Kybernetika-SPSE/RP_Psutka_Slepicka/škola_info/reporty/Slepička/2024_12_20.pdf

# RP report

Frantiˇsek Slepiˇcka

20.12.2024

Aktu´alnˇe m´ame jen jedno ESP32 (p˚ujˇcen´y) bez UWB modulu, proto pracuji na k´odu pro lokalizaci prostˇrednictv´ım WiFi (branch wifi). Vˇetˇsina k´odu je zkop´ırovan´y EPS-IDF example na wifi-scan.

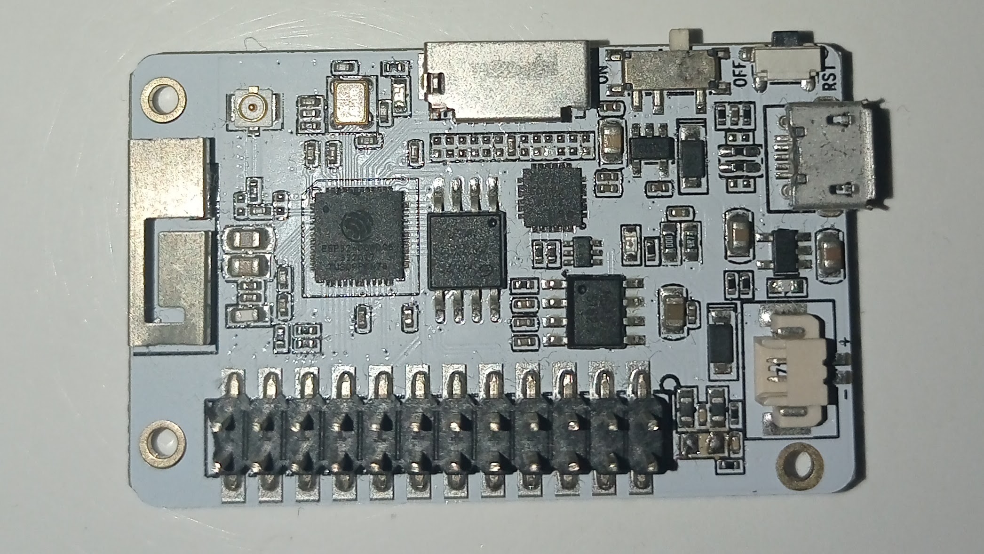
[picture p25: figure]

Figure 1: ESP

1
