Kybernetika-SPSE/RP_Psutka_Slepicka/škola_info/reporty/Slepička/2025_3_28.pdf

# RP report

František Slepička

28.3.2025

## 1 PCB

Už dorazily, takže jen zbývá nakoupit headry a nechat Matěje ať to tam napájí.

## 2 Kód

Nějak celý měsíc jsem programoval trilateraci pro navigace s UWB. Možná to nezní jako práce na celý měsíc, ale věřte mi, opravdu to zabralo celý měsíc. Všechen je na branchi wifi v RP Psutka Slepicka/src/UWB tracing logic/src/ (https://github.com/Kybernetika-SPSE/RP_Psutka_Slepicka/tree/wifi/src/UWB_tracing_logic/src) Pro samotnou trilateraci používám least square a výsledek z toho filtruji kalmanovým fitrem. Program je schopen dynamicky přepínat mezi řešením ve 2D či 3D na základě vstupních dat. Je to pravděpodobně zbytečně složité pro náš jednoduchý problém, avšak už jsem si zvykl dělat vše co nejvíc univerzální, aby to fungovalo i v jiných situacích. Tímto přístupem je projekt snadno rozšiřitelný do budoucna.

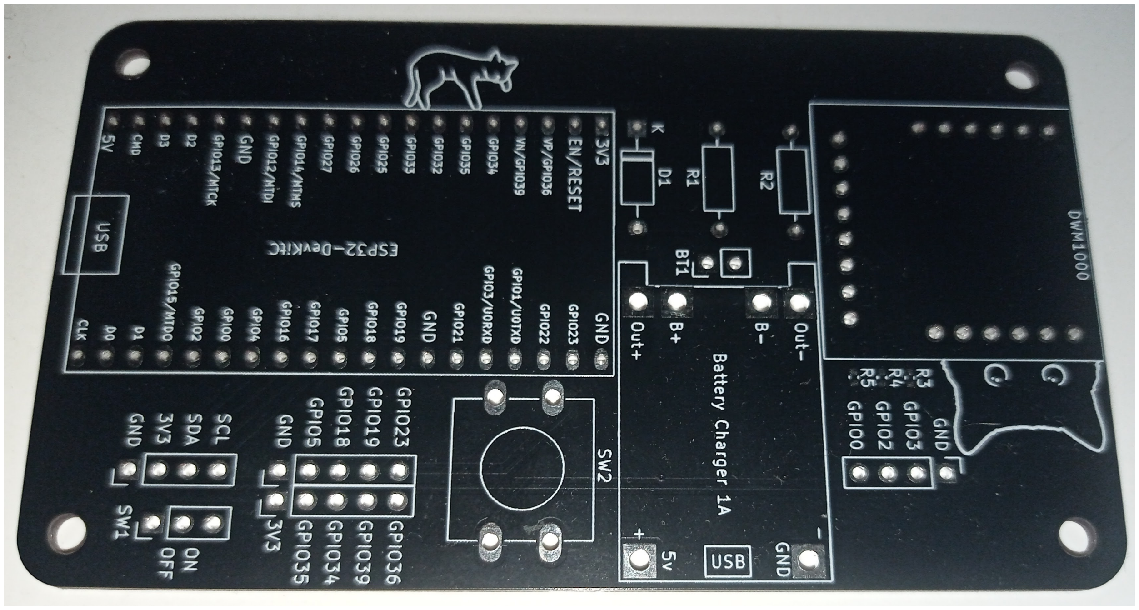
[picture p26: figure]

Figure 1: PCB

1
