Kybernetika-SPSE/RP_Psutka_Slepicka/src/main/src/serial_control/serial_control.h

#ifndef SERIAL_CONTROL_H
#define SERIAL_CONTROL_H
#include <Arduino.h>
#include "config.h"
#include "UWB_tracking_logic/trilateration.h"
#include "wifi_connection/wifi_connection.h"
#include "wifi_location/wifi_location.h"
#include "UWB/UWB.h"

void handleSerialInput();
#endif
