Kybernetika-SPSE/RP_Psutka_Slepicka/src/main/src/UWB_tracking_logic/matrix.h

#ifndef MATRIX_H
#define MATRIX_H

#include <Arduino.h>
#include <vector>

class Matrix
{
public:
    std::vector<std::vector<float>> matrix;

    Matrix();
    Matrix(int row, int col);
    Matrix(std::vector<std::vector<float>> input);

    int rows() const;
    int cols() const;

    Matrix operator*(const Matrix &other) const;
    void operator*=(float val);
    Matrix operator*(float val) const;

    std::vector<float> &operator[](int row);
    const std::vector<float> &operator[](int row) const;
    Matrix getColumn(int colIndex) const;
    void setColumn(int colIndex, const Matrix &col);

    Matrix operator+(const Matrix &other) const;
    Matrix operator-(const Matrix &other) const;

    void print() const;

    void set_value(float val);
    void set_identity(float scale = 1, int size = 0, int y = 0, int x = 0);
    
    float norm() const;
    Matrix transpose() const;
    Matrix gaussJordanInverse() const;

    std::pair<Matrix, Matrix> qrDecomposition() const;
    Matrix inverseQR() const;
};

#endif // MATRIX_H
